ElectronicCats/Badge-bsides-cdmx-2025/firmware/User/main.h

#ifndef __MAIN_H
#define __MAIN_H

#ifdef __cplusplus
extern "C" {
#endif

#include "py32f0xx_ll_bus.h"
#include "py32f0xx_ll_cortex.h"
#include "py32f0xx_ll_dma.h"
#include "py32f0xx_ll_exti.h"
#include "py32f0xx_ll_gpio.h"
#include "py32f0xx_ll_pwr.h"
#include "py32f0xx_ll_rcc.h"
#include "py32f0xx_ll_i2c.h"
#include "py32f0xx_ll_spi.h"
#include "py32f0xx_ll_system.h"
#include "py32f0xx_ll_tim.h"
#include "py32f0xx_ll_utils.h"

uint8_t SPI_TxRxByte(uint8_t data);
void APP_ErrorHandler(void);
void APP_I2C_Transmit(uint8_t devAddress, uint8_t memAddress, uint8_t *pData, uint16_t len);

#ifdef __cplusplus
}
#endif

#endif /* __MAIN_H */
