ElectronicCats/Badge-bsides-cdmx-2025/firmware/User/ws2812_spi.h

#ifndef __WS2812_SIP_H
#define __WS2812_SIP_H

#ifdef __cplusplus
extern "C" {
#endif

#include "main.h"

#define WS2812_NUM_LEDS 2
#define WS2812_SPI_HANDLE Spi1Handle

#define WS2812_RESET_PULSE 60
#define WS2812_BUFFER_SIZE (WS2812_NUM_LEDS * 24 + WS2812_RESET_PULSE)

#define WS2812_SPI_TxRxByte(__DATA__)   SPI_TxRxByte(__DATA__)

/**
 * @brief Value from 0 to 255
 */
#define DEFAULT_BRIGHTNESS 10

extern uint8_t ws2812_buffer[];
// extern uint8_t _brightness;

void ws2812_init(void);
void ws2812_send_spi(void);
void ws2812_pixel(uint16_t led_no, uint8_t r, uint8_t g, uint8_t b);
void ws2812_pixel_all(uint8_t r, uint8_t g, uint8_t b);

/**
 * @brief Set the brightness of the WS2812 LEDs.
 * 
 * @param brightness Value from 0 to 255, where 0 is off and 255 is full brightness.
 */
void ws2812_set_brightness(uint8_t brightness);

#ifdef __cplusplus
}
#endif

#endif /* __WS2812_SIP_H */
